TheNooB2706/zydp-minipad/images/IMG_20240310_164629.jpg

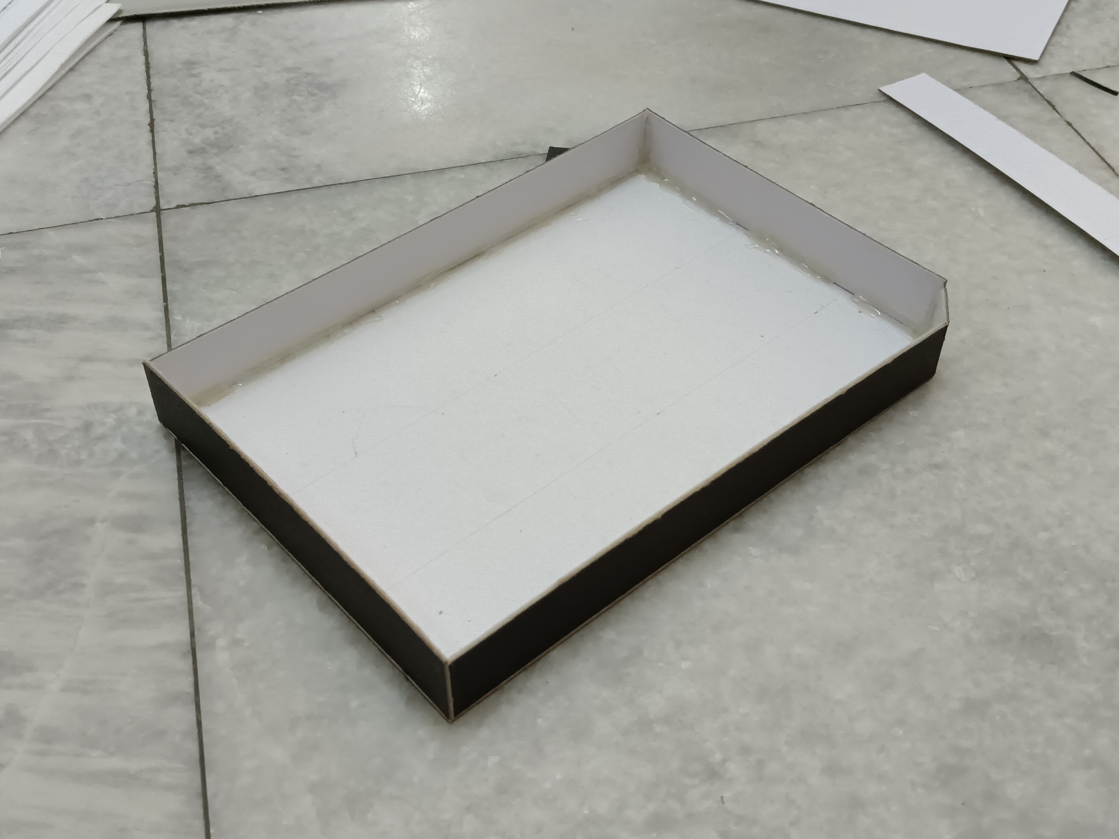
images/IMG_20240310_164629.jpg
