TheNooB2706/zydp-minipad/images/IMG_20240310_170240.jpg

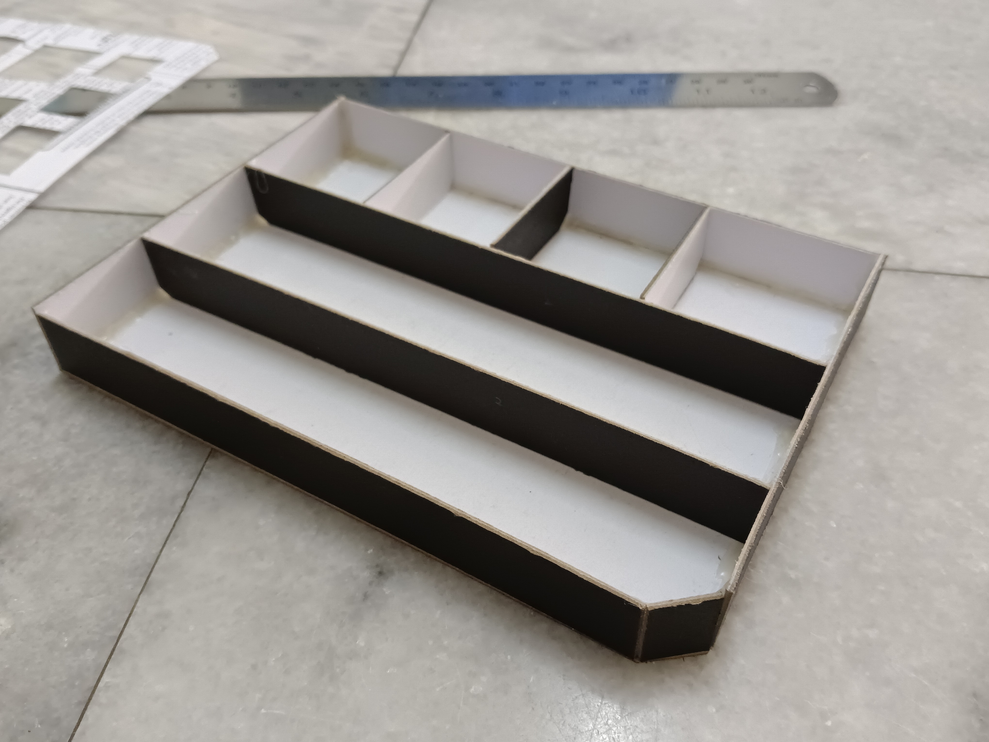
images/IMG_20240310_170240.jpg
