TheNooB2706/zydp-minipad/images/IMG_20240312_233155.jpg

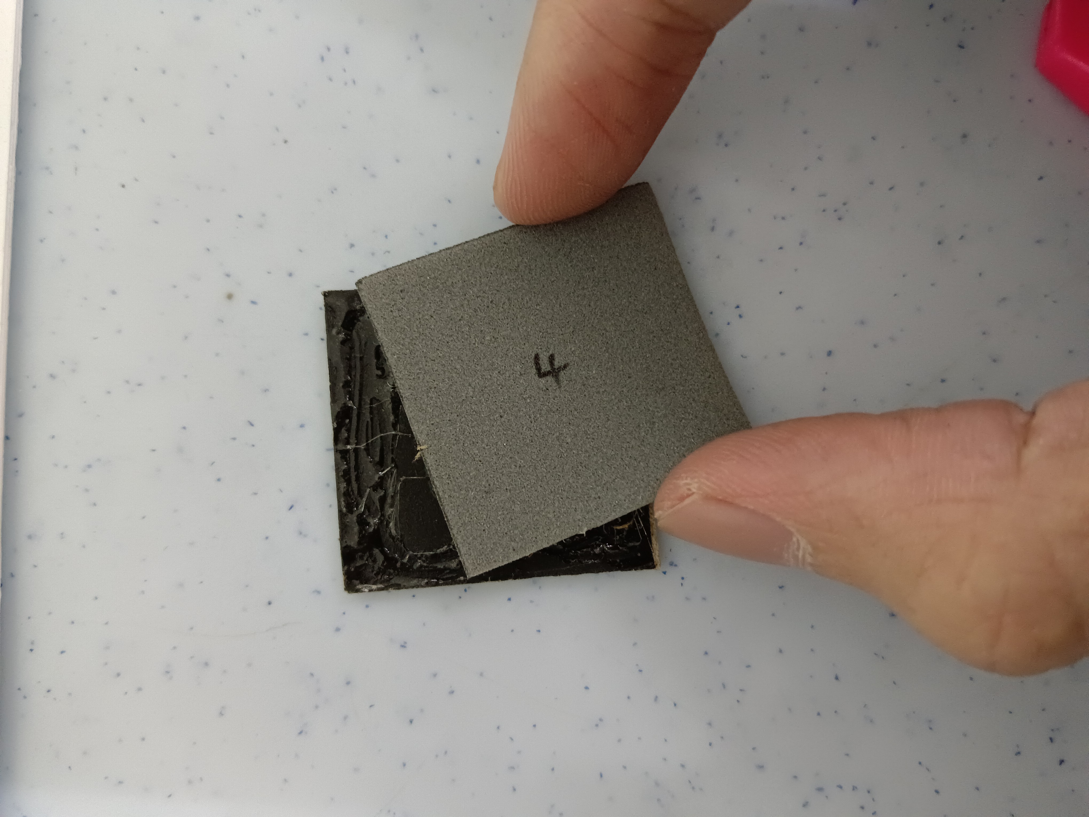
images/IMG_20240312_233155.jpg
