TheNooB2706/zydp-minipad/images/IMG_20240312_233313.jpg

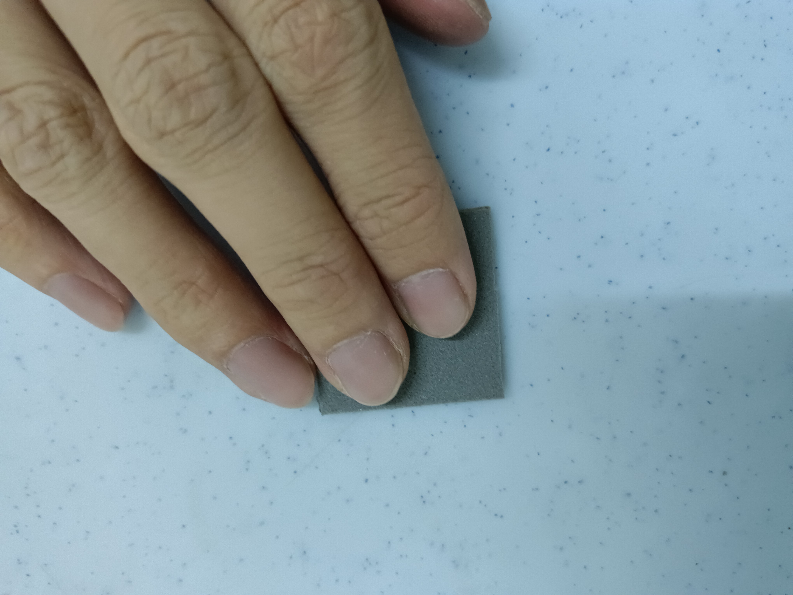
images/IMG_20240312_233313.jpg
