TheNooB2706/zydp-minipad/images/IMG_20240318_154917.jpg

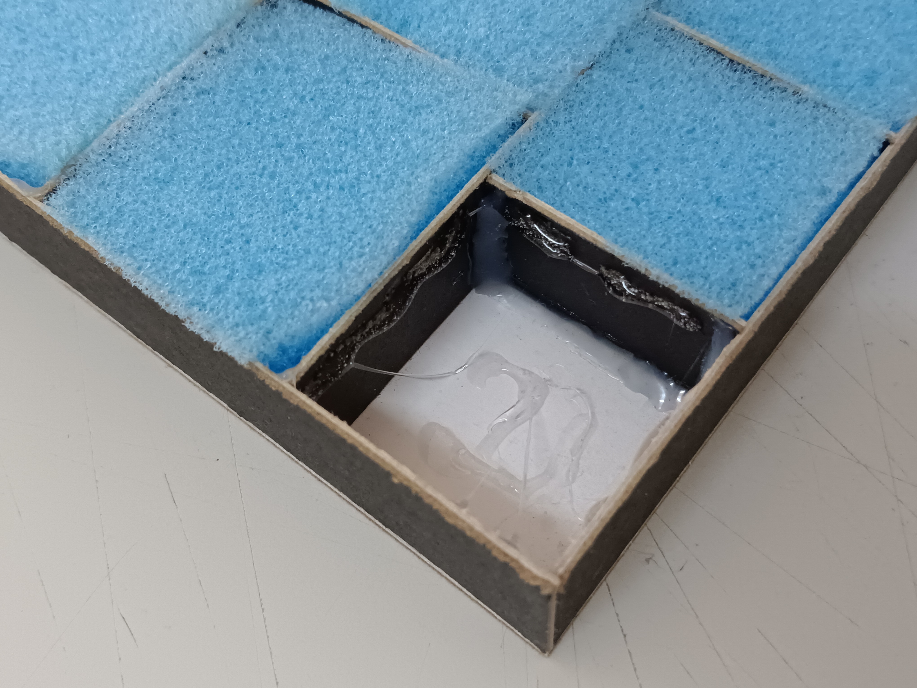
images/IMG_20240318_154917.jpg
