TheNooB2706/zydp-minipad/images/IMG_20240320_110717.jpg

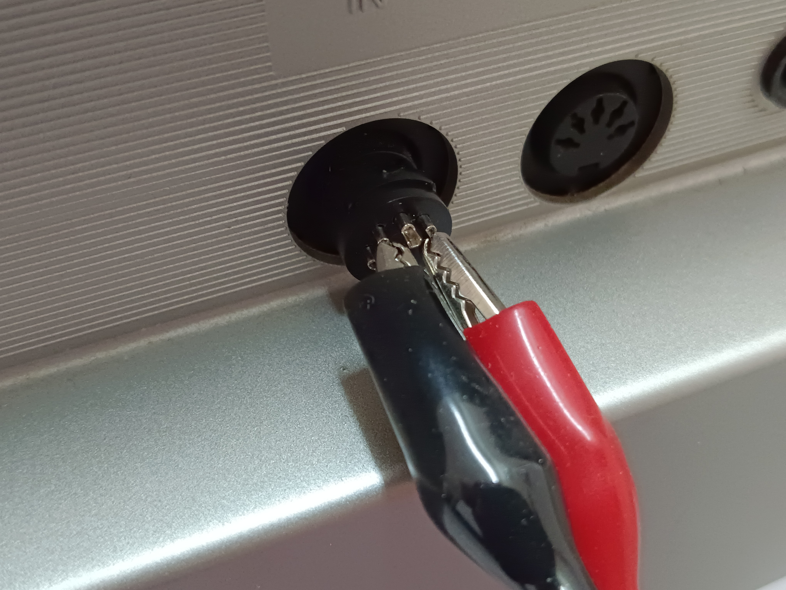
images/IMG_20240320_110717.jpg
