TheNooB2706/zydp-minipad/images/IMG_20240321_000928.jpg

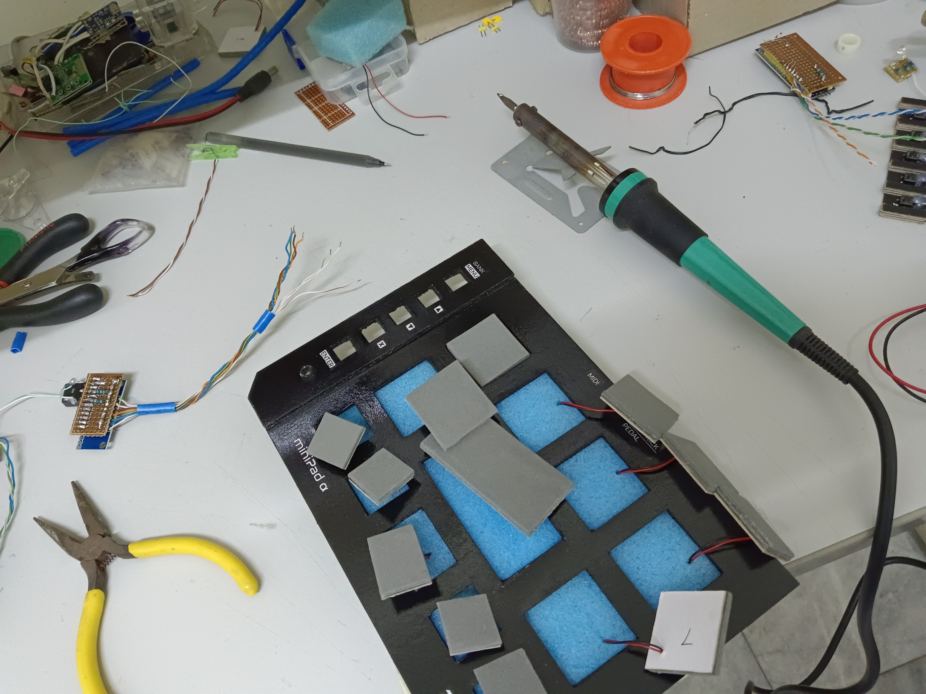
images/IMG_20240321_000928.jpg
