TheNooB2706/zydp-minipad/images/IMG_20240321_105618_3.jpg

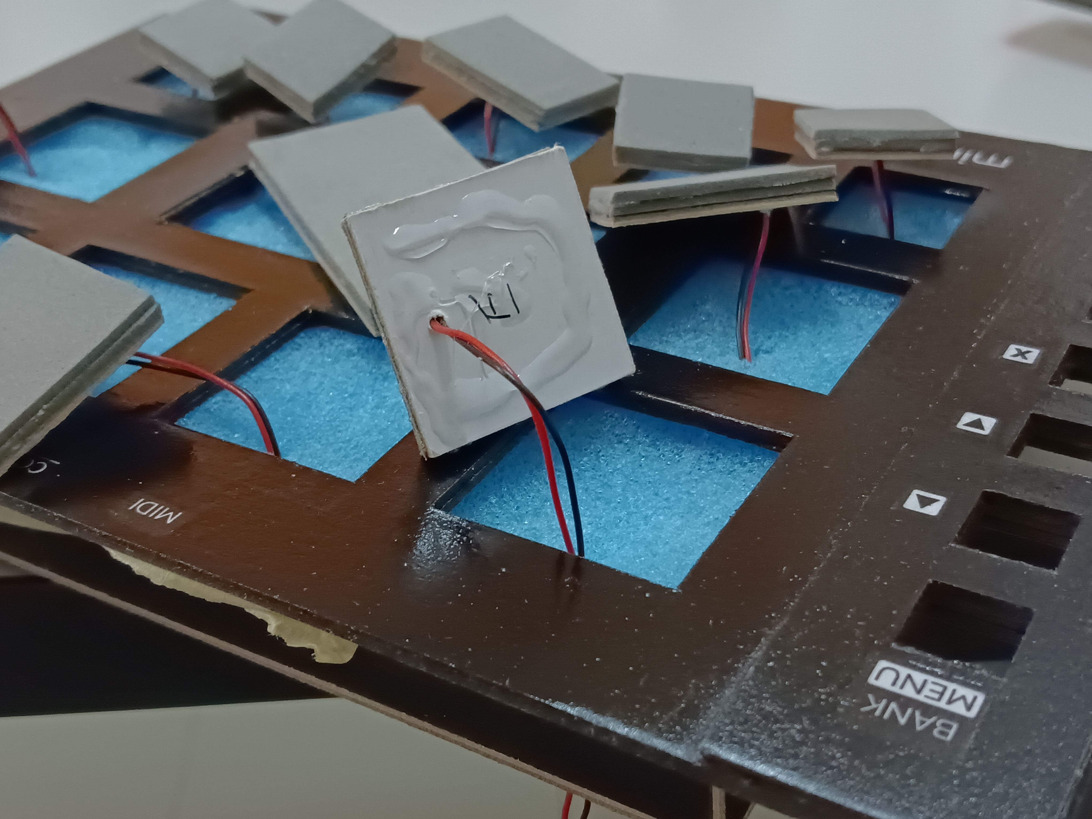
images/IMG_20240321_105618_3.jpg
