TheNooB2706/zydp-minipad/images/IMG_20240321_105719.jpg

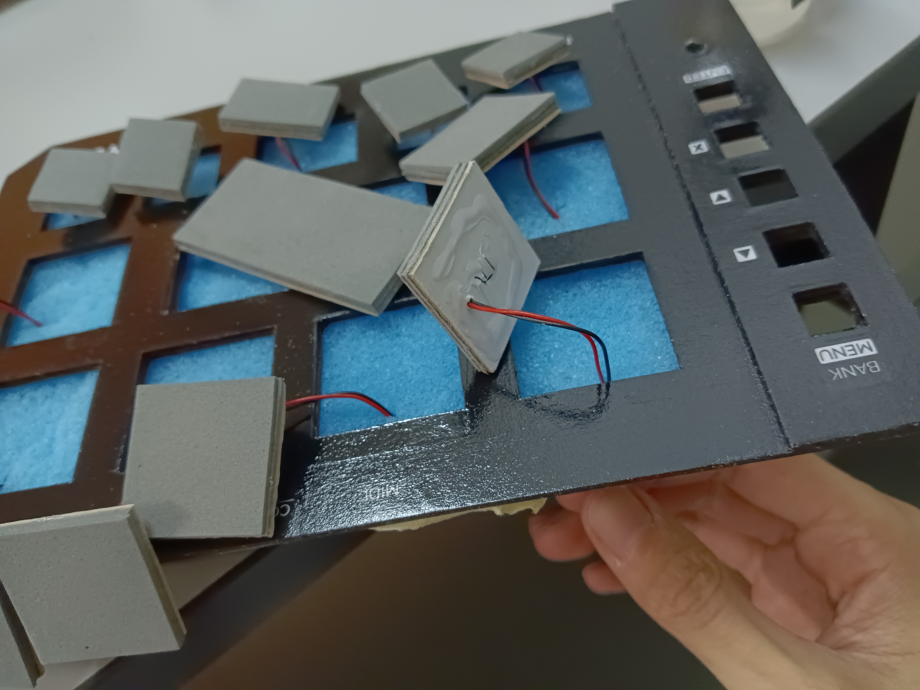
images/IMG_20240321_105719.jpg
