TheNooB2706/zydp-minipad/images/IMG_20240322_132838.jpg

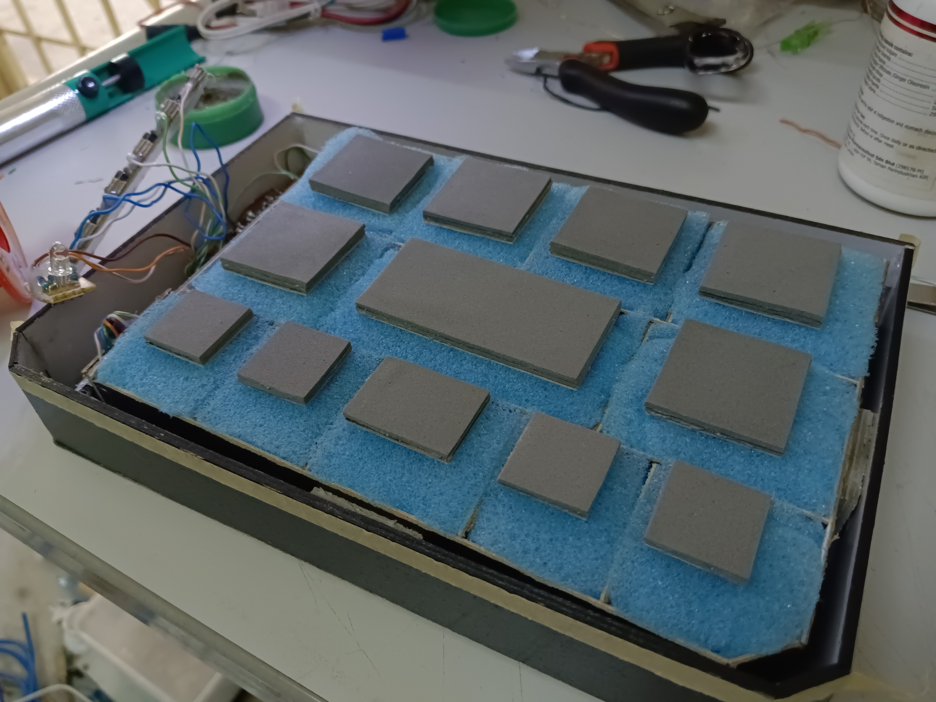
images/IMG_20240322_132838.jpg
