TheNooB2706/zydp-minipad/images/IMG_20240322_154246.jpg

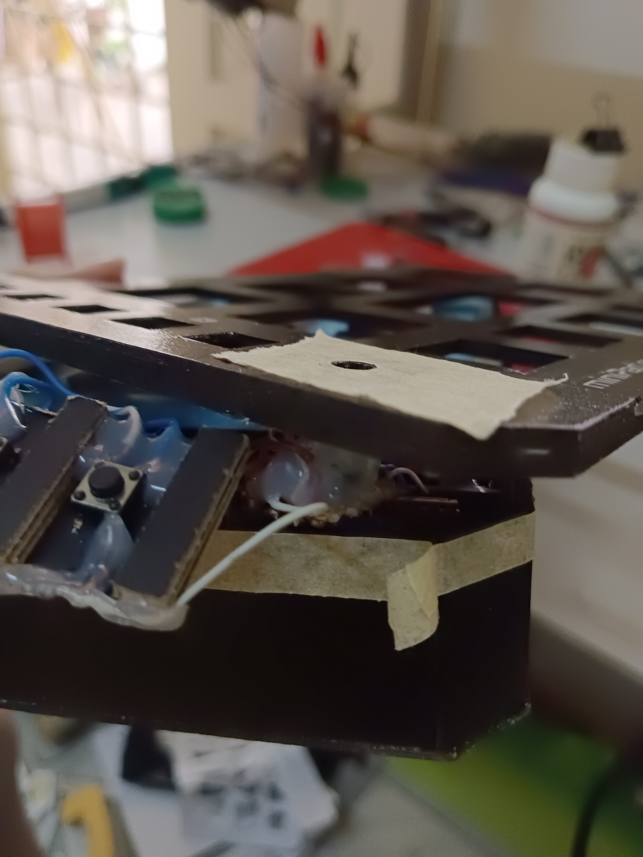
images/IMG_20240322_154246.jpg
