TheNooB2706/zydp-minipad/schematic/schematic.kicad_sch

## KiCad design schematic/schematic.kicad_sch (2024-09-14)

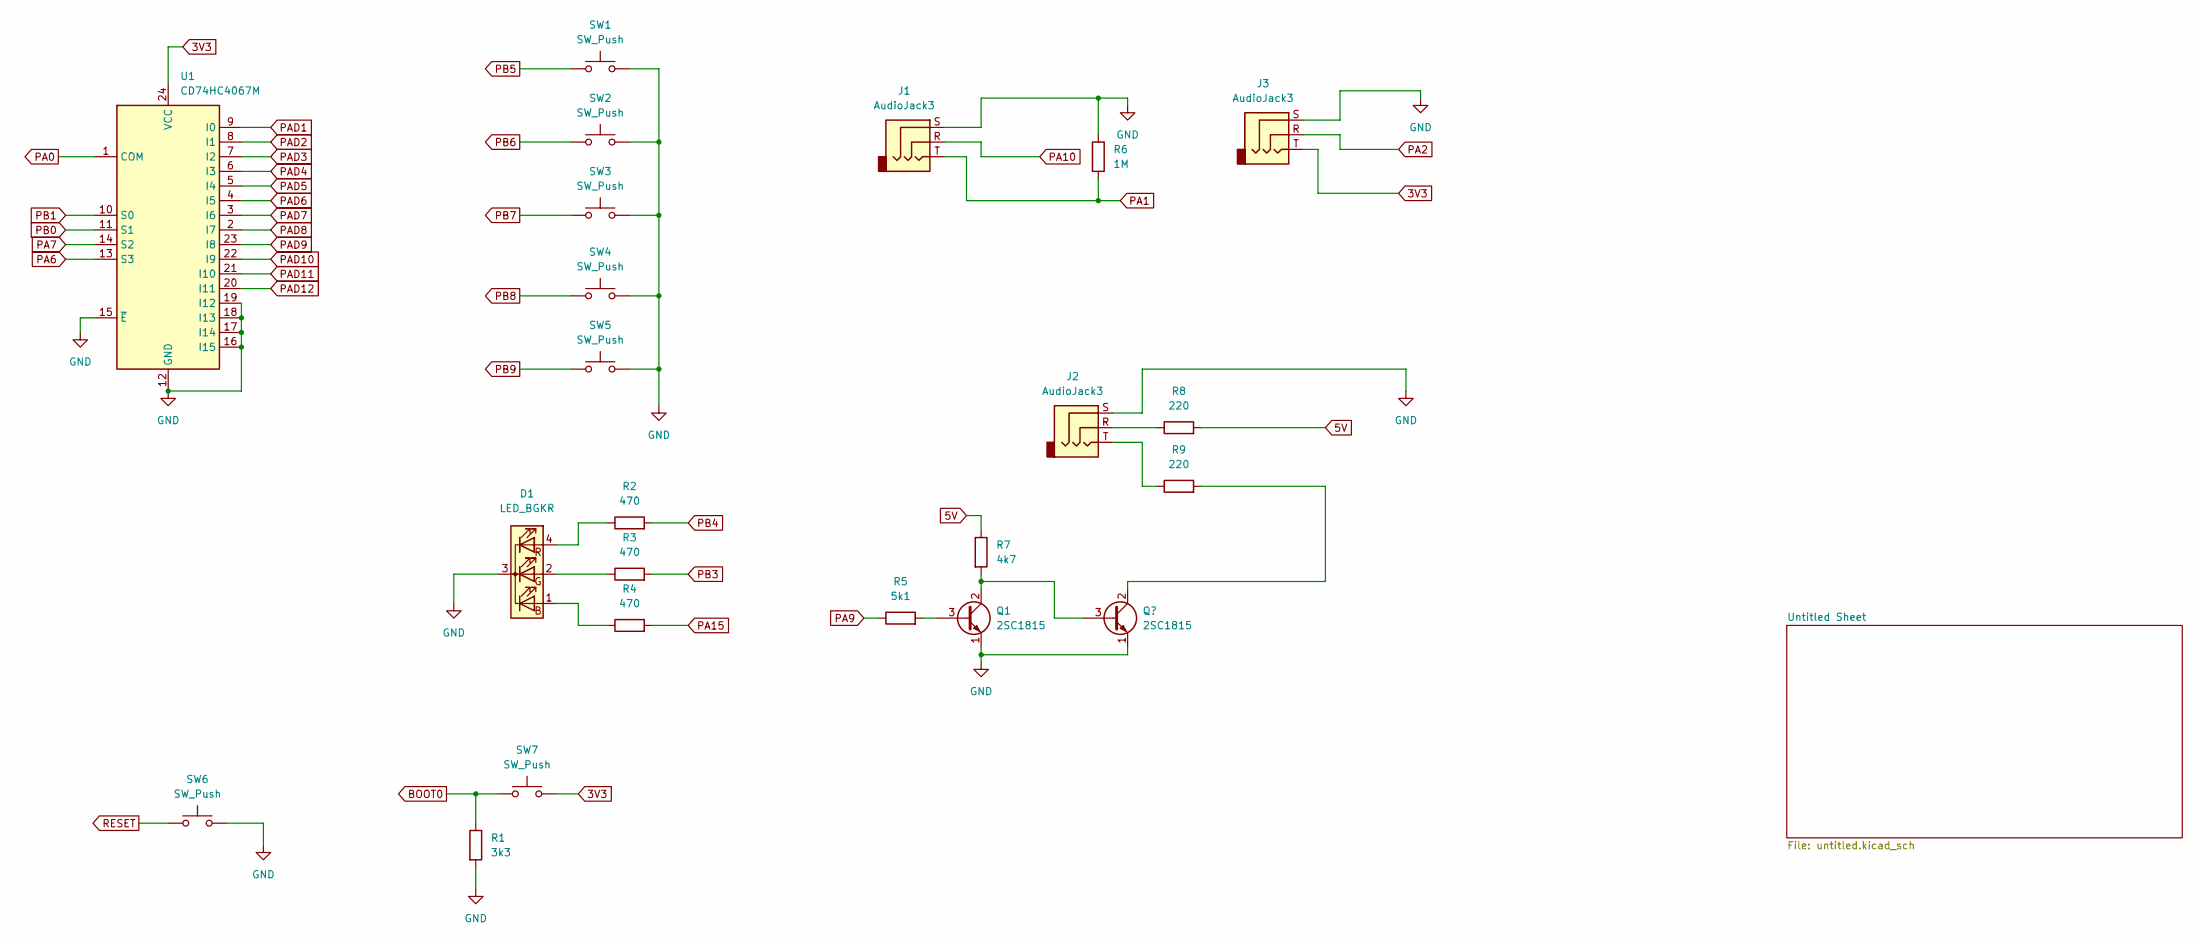
[picture p57: schematic schematic.kicad_sch]

Parts:
D1: LED_BGKR
J1, J2, J3: AudioJack3
Q1: 2SC1815; TO-92_Inline
R1: 3k3
R2, R3, R4: 470
R5: 5k1
R6: 1M
R7: 4k7
R8, R9: 220
SW1, SW2, SW3, SW4, SW5, SW6, SW7: SW_Push
U1: CD74HC4067M; SOIC-24W_7.5x15.4mm_P1.27mm

Connections:
3V3: J3.T, SW7.2, U1.24 (VCC)
5V: R7.1, R8.2
BOOT0: R1.1, SW7.1
GND: D1.3 (K), J1.S, J2.S, J3.S, Q1.1 (E), R1.2, R6.1, SW1.2, SW2.2, SW3.2, SW4.2, SW5.2, SW6.2, U1.12 (GND), U1.15 (~E), U1.16 (I15), U1.17 (I14), U1.18 (I13), U1.19 (I12)
unnamed: D1.1 (BA), R4.1
unnamed: D1.2 (GA), R3.1
unnamed: D1.4 (RA), R2.1
unnamed: J2.R, R8.1
unnamed: J2.T, R9.1
unnamed: Q1.2 (C), R7.2
unnamed: Q1.3 (B), R5.2
PA0: U1.1 (COM)
PA1: J1.T, R6.2
PA2: J3.R
PA6: U1.13 (S3)
PA7: U1.14 (S2)
PA9: R5.1
PA10: J1.R
PA15: R4.2
PAD1: U1.9 (I0)
PAD2: U1.8 (I1)
PAD3: U1.7 (I2)
PAD4: U1.6 (I3)
PAD5: U1.5 (I4)
PAD6: U1.4 (I5)
PAD7: U1.3 (I6)
PAD8: U1.2 (I7)
PAD9: U1.23 (I8)
PAD10: U1.22 (I9)
PAD11: U1.21 (I10)
PAD12: U1.20 (I11)
PB0: U1.11 (S1)
PB1: U1.10 (S0)
PB3: R3.2
PB4: R2.2
PB5: SW1.1
PB6: SW2.1
PB7: SW3.1
PB8: SW4.1
PB9: SW5.1
RESET: SW6.1
