TheNooB2706/zydp-minipad/schematic/untitled.kicad_sch

## KiCad design schematic/untitled.kicad_sch (2024-09-14)

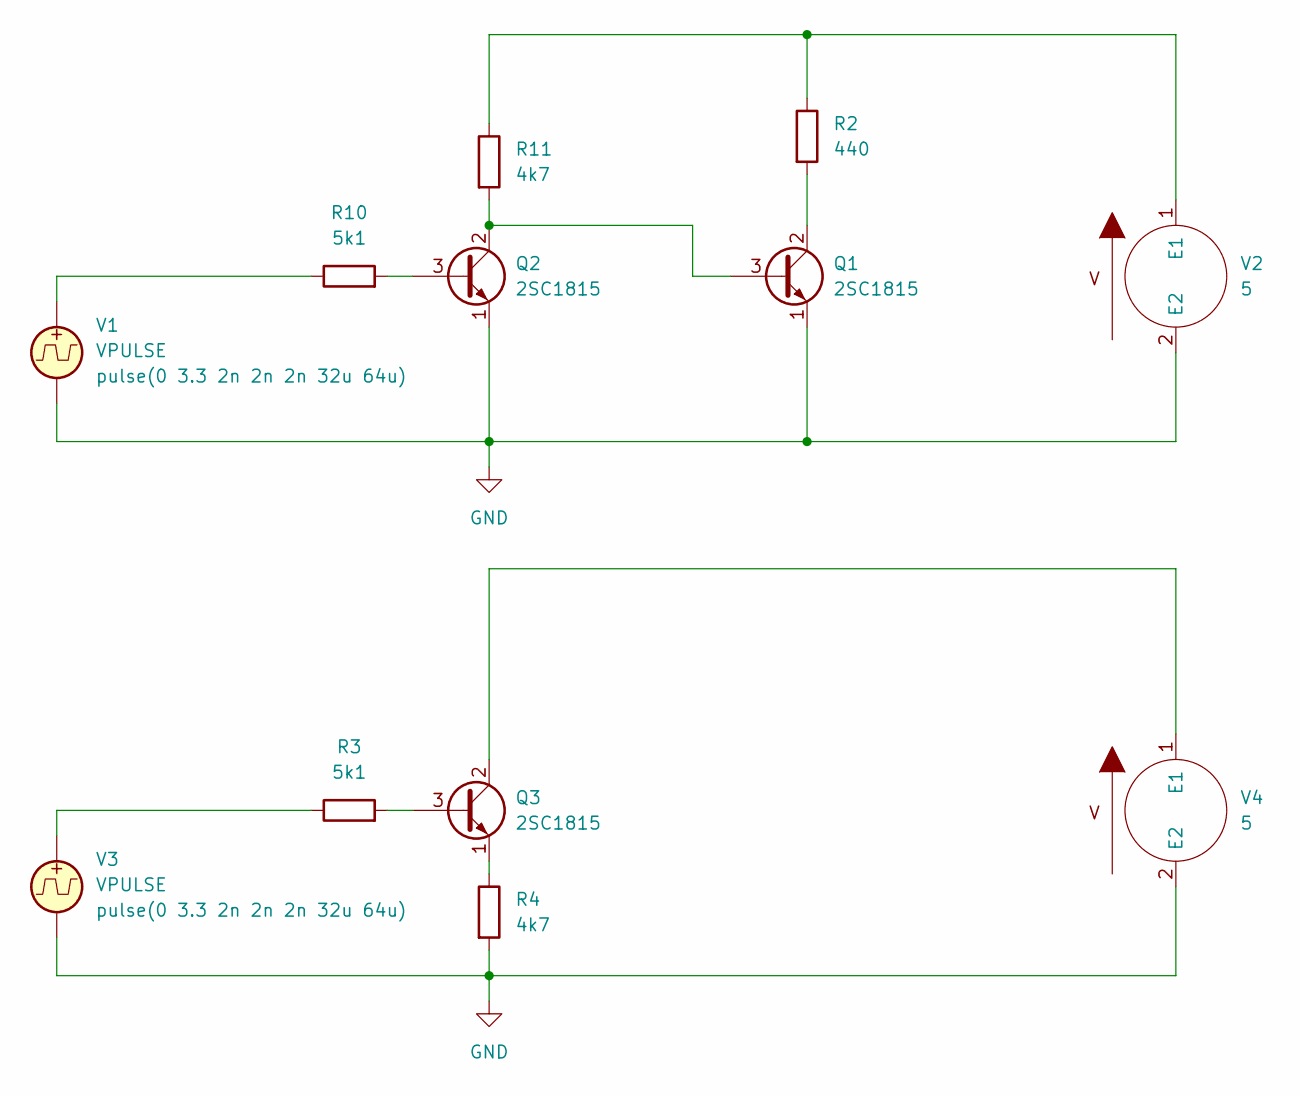
[picture p58: schematic untitled.kicad_sch]

Parts:
Q1, Q2, Q3: 2SC1815; TO-92_Inline
R2: 440
R3, R10: 5k1
R4, R11: 4k7
V1, V3: VPULSE
V2, V4: 5

Connections:
GND: Q1.1 (E), Q2.1 (E), R4.2, V1.2, V2.2 (E2), V3.2, V4.2 (E2)
unnamed: Q1.2 (C), R2.2
unnamed: Q1.3 (B), Q2.2 (C), R11.2
unnamed: Q2.3 (B), R10.2
unnamed: Q3.1 (E), R4.1
unnamed: Q3.2 (C), V4.1 (E1)
unnamed: Q3.3 (B), R3.2
unnamed: R3.1, V3.1
unnamed: R10.1, V1.1
unnamed: R2.1, R11.1, V2.1 (E1)
